JBlitzar/stor/doc/tps_schem.png

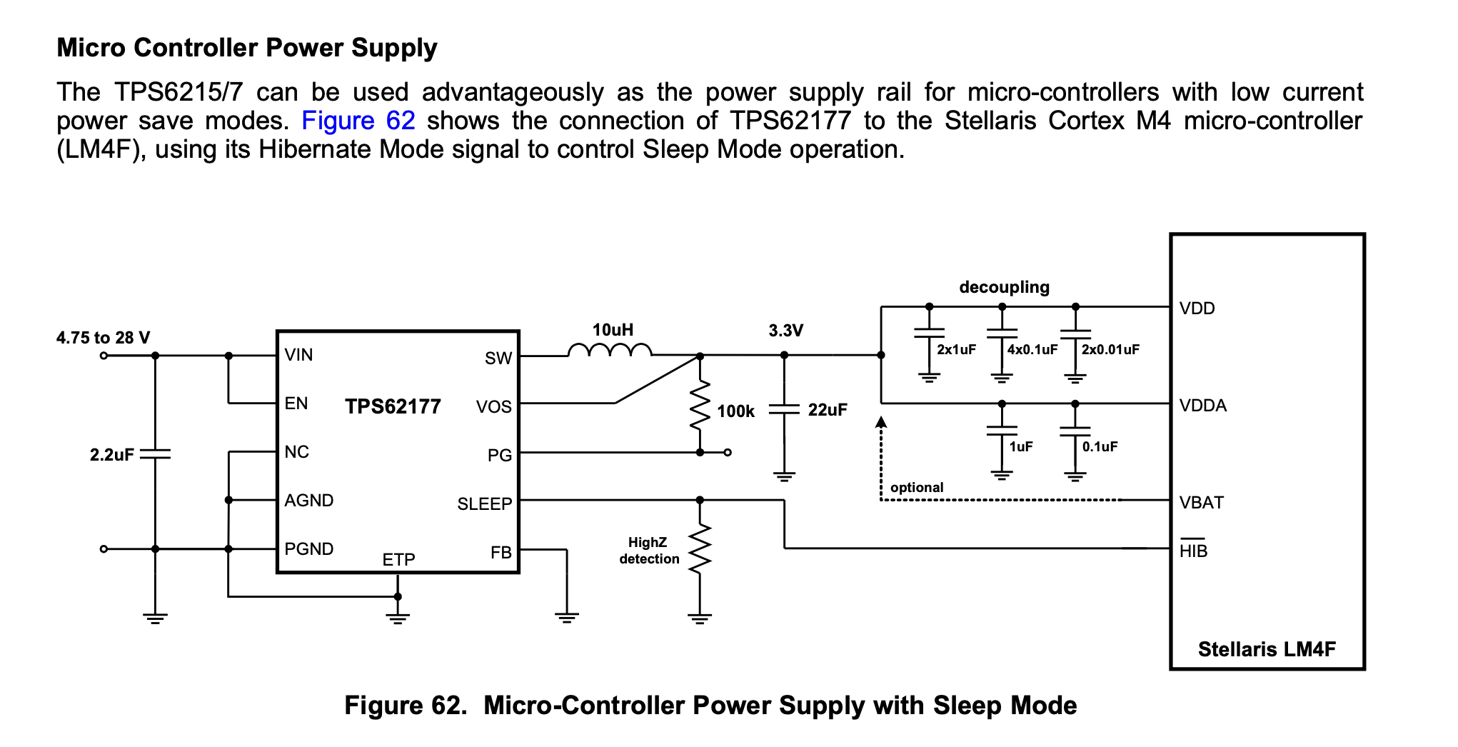
doc/tps_schem.png
