JBlitzar/stor/PCB/stor/production_v1/fab_shot.png

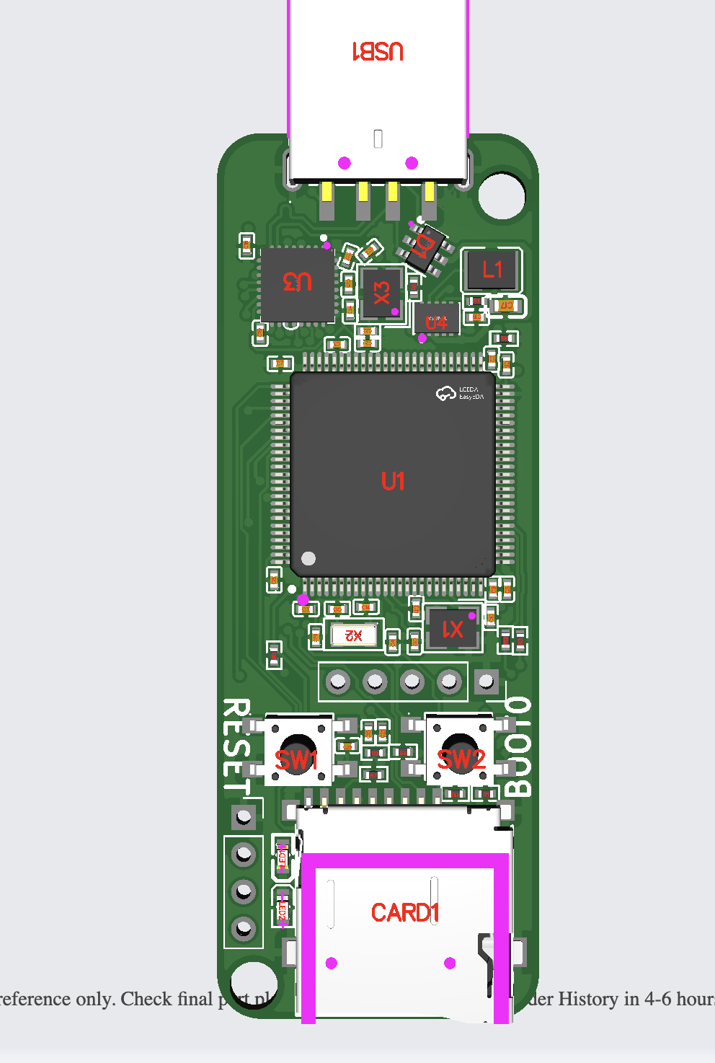
PCB/stor/production_v1/fab_shot.png
